r2b5/Arduboy-Version-2/pics/ArduinoISP.jpg

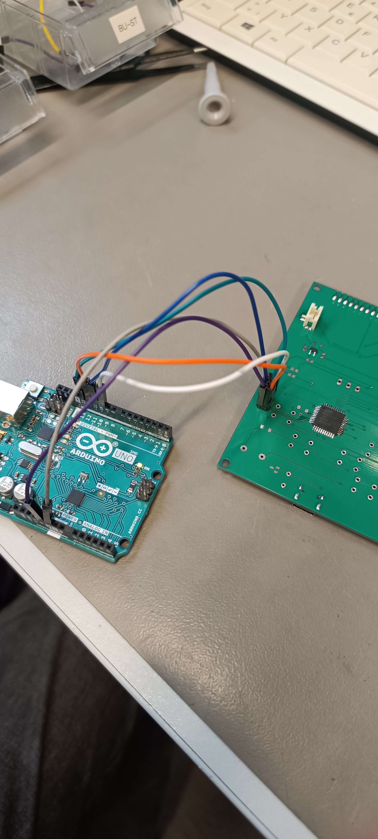
pics/ArduinoISP.jpg
