r2b5/Arduboy-Version-2/src/Tetris/Tetris.ino

#include <Arduboy2.h>

#include "shapes.h"
#include "grid.h"
#include "input_handler.h"

using namespace std;

static Arduboy arduboy;

static shape_actor_t current_actor;

static Grid grid;
static InputHandler input_handler;

static unsigned long time_started;
static unsigned long last_update;

static const unsigned long kDroppingBlockSpeed = 12.0;
static const unsigned long kFallingBlockSpeed = 1.0;

static unsigned long block_speed = kFallingBlockSpeed;

static unsigned int current_score = 0;
bool game_over = false;
uint8_t restartPresses = 0;
bool pause = false;

tetromino_t* random_tetromino()
{
    static const unsigned int num_tetrominos = 8;
    tetromino_t *tetrominos[num_tetrominos] = {
        &SquareBlock,
        &LeftLBlock,
        &RightLBlock,
        &LongBlock,
        &MountainBlock,
        &ZBlock,
        &SBlock,
        &SquareBigBlock,
    };

    long random_idx = random(num_tetrominos);
    return tetrominos[random_idx];
}
void restart_game()
{
    current_score = 0;
    game_over = false;
    restartPresses = 0;
    pause = false;

    block_speed = kFallingBlockSpeed;

    grid.reset();

    current_actor.position = { 5, 0 };
    current_actor.tetromino = random_tetromino();
    current_actor.rotation = 0;
}

void next_block()
{
    grid.commit_actor(current_actor);

    unsigned int lines_cleared = grid.clear_lines();

    switch (lines_cleared)
{
    case 1:
        current_score += 40;
        break;

    case 2:
        current_score += 100;
        break;

    case 3:
        current_score += 300;
        break;

    case 4:
        current_score += 1200;   // TETRIS!
        break;
}

    current_actor.position = { 5, 0 };
    current_actor.tetromino = random_tetromino();
    current_actor.rotation = 0;

    if (grid.actor_collides(current_actor)) {
        game_over = true;
    }
}

void move_current_block_down()
{
    shape_actor_t ghost_actor(current_actor);
    ghost_actor.position.y += 1;

    if (grid.actor_collides(ghost_actor)) {
        next_block();
    } else {
        current_actor.position = ghost_actor.position;
    }
}

void button_handler(uint8_t button, bool down)
{
   if (game_over) {
    if (down && button == A_BUTTON) {
        restartPresses++;

        if (restartPresses >= 2) {
            restart_game();
        }
    }
    return;
}

if (down && button == UP_BUTTON && !game_over)
{
    pause = !pause;
    return;
}

    shape_actor_t ghost_actor(current_actor);

    if (down && button == RIGHT_BUTTON) {
        ghost_actor.position.x += 1;
    }

    if (down && button == LEFT_BUTTON) {
        ghost_actor.position.x -= 1;
    }

    if (down && button == A_BUTTON) {
        ghost_actor.rotation -= 1;
    }

    if (down && button == B_BUTTON) {
        ghost_actor.rotation += 1;
    }

    if (button == DOWN_BUTTON) {
        if (down) {
            block_speed = kDroppingBlockSpeed;
        } else {
            block_speed = kFallingBlockSpeed;
        }
    }

    if (!grid.actor_collides(ghost_actor)) {
        current_actor.position = ghost_actor.position;
        current_actor.rotation = ghost_actor.rotation;
    }
}

void draw_hud(int16_t xpos, int16_t ypos)
{
    const unsigned int kLineHeight = 8;

    arduboy.setTextSize(1);
    arduboy.setCursor(xpos, ypos);

    arduboy.print("Ardutris");

    ypos += kLineHeight + 8;
    arduboy.setCursor(xpos, ypos);

    const char *scoreText = "SCORE";
    arduboy.print(scoreText);

    ypos += kLineHeight;
    arduboy.setCursor(xpos, ypos);

    char scoreString[16];
    sprintf(scoreString, "%u", current_score);
    arduboy.print(scoreString);

    if (game_over) {
        ypos += kLineHeight * 2;
        arduboy.setCursor(xpos, ypos);

        arduboy.print("GAME OVER");
    }

    if (pause)
    {
    ypos += 16;
    arduboy.setCursor(xpos, ypos);
    arduboy.print("PAUSE");
    }
}

void update(unsigned long dt)
{
    input_handler.handle_input(arduboy);

    if (!game_over && !pause)
{
        unsigned long now = millis();
        static unsigned long last_movement = 0;
        if ( (now - last_movement) > (1000 / block_speed) ) {
            // Every second, move interactive actor down by one block
            move_current_block_down();

            last_movement = now;
        }
    }
}

void draw(unsigned long dt)
{
    arduboy.clear();
    arduboy.fillScreen(BLACK);

    Grid display_grid;
    display_grid.copy(grid);

    // Put current actor onto the display grid
    display_grid.commit_actor(current_actor);

    display_grid.draw(arduboy, 20, 2);

    draw_hud(65, 5);

    arduboy.display();
}

void setup()
{
    randomSeed(analogRead(0));

    arduboy.begin();
    arduboy.setFrameRate(60);

    time_started = millis();
    last_update = time_started;

    input_handler.button_handler = button_handler;

    restart_game();
}

void loop()
{
    unsigned long now = millis();
    update(now - last_update);
    draw(now - last_update);
    last_update = now;
}
