r2b5/Arduboy-Version-2/src/arduware-master/arduboy_game/minigame_hurdles.h

#ifndef MINIGAME_HURDLES_H
#define MINIGAME_HURDLES_H

#include "globals.h"
#include <Arduboy2.h>
#include <ArduboyTones.h>

extern Arduboy2 arduboy;
extern ArduboyTones sound;
extern int score;

void doHurdlesGame();

#endif
