r2b5/Arduboy-Version-2/src/Tetris/shapes.h

#ifndef SHAPES_H
#define SHAPES_H

#include "utils.h"

#define SHAPE_BOUNDS_WIDTH  4
#define SHAPE_BOUNDS_HEIGHT 4
#define SHAPE_SIZE (SHAPE_BOUNDS_HEIGHT * SHAPE_BOUNDS_WIDTH)

#define AT(x, y) (SHAPE_BOUNDS_WIDTH * y + x)

struct tetromino_t {
    unsigned int width;
    unsigned int height;

    int shape_data[SHAPE_SIZE];

    int at(unsigned int x, unsigned int y) {
        if (x >= width) return 0;
        if (y >= height) return 0;

        return shape_data[AT(x, y)];
    }

    // returns rotated position offset
    point_t rotated_shape_data(const int rotation, int (*result_shape_data)[16]);
};

static tetromino_t SquareBlock = {
    .width = 2,
    .height = 2,
    .shape_data = {
        1, 1, 0, 0,
        1, 1, 0, 0,
        0, 0, 0, 0,
        0, 0, 0, 0,
    },
};


static tetromino_t SquareBigBlock = {
    .width = 2,
    .height = 3,
    .shape_data = {
        1, 1, 0, 0,
        1, 1, 0, 0,
        1, 1, 0, 0,
        0, 0, 0, 0,
    },
};

static tetromino_t LeftLBlock = {
    .width = 2,
    .height = 3,
    .shape_data = {
        1, 0, 0, 0,
        1, 0, 0, 0,
        1, 1, 0, 0,
        0, 0, 0, 0,
    },
};

static tetromino_t RightLBlock = {
    .width = 2,
    .height = 3,
    .shape_data = {
        0, 1, 0, 0,
        0, 1, 0, 0,
        1, 1, 0, 0,
        0, 0, 0, 0,
    },
};

static tetromino_t LongBlock = {
    .width = 1,
    .height = 4,
    .shape_data = {
        1, 0, 0, 0,
        1, 0, 0, 0,
        1, 0, 0, 0,
        1, 0, 0, 0,
    },
};

static tetromino_t MountainBlock = {
    .width = 3,
    .height = 2,
    .shape_data = {
        0, 1, 0, 0,
        1, 1, 1, 0,
        0, 0, 0, 0,
        0, 0, 0, 0,
    },
};

static tetromino_t ZBlock = {
    .width = 3,
    .height = 2,
    .shape_data = {
        1, 1, 0, 0,
        0, 1, 1, 0,
        0, 0, 0, 0,
        0, 0, 0, 0,
    },
};

static tetromino_t SBlock = {
    .width = 3,
    .height = 2,
    .shape_data = {
        0, 1, 1, 0,
        1, 1, 0, 0,
        0, 0, 0, 0,
        0, 0, 0, 0,
    },
};

struct shape_actor_t
{
public:
    point_t      position;
    tetromino_t *tetromino;
    int          rotation = 0;

    shape_actor_t() {};
    shape_actor_t(const shape_actor_t& a)
        : position(a.position), tetromino(a.tetromino), rotation(a.rotation) {};
};

#endif
