r2b5/Arduboy-Version-2/src/arduware-master/arduboy_game/arduware_title_compressed.h

const uint8_t PROGMEM arduware_title_compressed[] = {
    0x7f, 0x3f, 0x80, 0x65, 0x68, 0xe7, 0xb6, 0xe9, 0x74, 0x76, 0x9d, 0x4e, 
    0x4b, 0x05, 0xbd, 0xa5, 0xe4, 0x36, 0x9d, 0x4e, 0xaa, 0xf0, 0x6c, 0xd3, 
    0xe9, 0x74, 0x9a, 0x7d, 0x3b, 0xb3, 0xdd, 0xa6, 0xd3, 0x5b, 0xe8, 0x39, 
    0xe7, 0xe2, 0xde, 0xb9, 0x6d, 0x1a, 0x41, 0x76, 0x44, 0xe9, 0xf8, 0x97, 
    0x2b, 0xe7, 0x94, 0x53, 0xf2, 0xd3, 0x4b, 0xda, 0x9d, 0x53, 0x32, 0x9d, 
    0x54, 0x4e, 0x2a, 0xc5, 0xfe, 0x5c, 0x2b, 0xb9, 0x4d, 0xa7, 0xb3, 0xbc, 
    0x6d, 0xb7, 0xe9, 0xb4, 0x57, 0x92, 0x9f, 0xcb, 0xcd, 0x9a, 0xd6, 0x29, 
    0x44, 0xb1, 0x2d, 0x95, 0x92, 0xdb, 0xed, 0x7a, 0xc2, 0xf4, 0x96, 0xd9, 
    0x86, 0x26, 0xe7, 0x76, 0x4a, 0x39, 0xa7, 0xe4, 0x4c, 0x69, 0x2e, 0x37, 
    0xe7, 0xce, 0x29, 0x47, 0x94, 0xde, 0xa2, 0x37, 0xe7, 0xc2, 0x95, 0x52, 
    0x52, 0x49, 0x25, 0x95, 0x74, 0x8e, 0x5f, 0x49, 0xba, 0x14, 0xc2, 0x90, 
    0x48, 0x4f, 0x9b, 0x22, 0xe7, 0xc3, 0x93, 0x73, 0x52, 0x29, 0x14, 0x1d, 
    0xad, 0x92, 0x76, 0x5c, 0x39, 0x1d, 0xb6, 0x9e, 0x50, 0xc6, 0xa9, 0x94, 
    0xdc, 0xa2, 0x88, 0x17, 0x53, 0x4a, 0x91, 0xa7, 0x23, 0x46, 0xd1, 0x76, 
    0xbb, 0xdc, 0xb9, 0xed, 0x18, 0xdd, 0x39, 0xe7, 0x9c, 0x73, 0xce, 0x39, 
    0xa7, 0x90, 0xe7, 0x9c, 0x73, 0x4a, 0x2a, 0x39, 0x9b, 0x73, 0xce, 0x29, 
    0xa9, 0xa4, 0x92, 0xdb, 0xd0, 0xb9, 0x55, 0xd2, 0x39, 0xe7, 0x9c, 0x73, 
    0x4e, 0x49, 0x25, 0x9d, 0x73, 0x4e, 0x91, 0x6e, 0x95, 0x74, 0xce, 0x39, 
    0xe7, 0x9c, 0x73, 0x6e, 0xeb, 0x9c, 0x73, 0x0e, 0x67, 0x5b, 0xe7, 0x9c, 
    0x53, 0x48, 0x52, 0xd2, 0x39, 0xe7, 0xa2, 0x57, 0xd2, 0x39, 0x27, 0x95, 
    0x5c, 0x6e, 0x9d, 0x73, 0xce, 0xb9, 0x78, 0x95, 0x73, 0xce, 0x39, 0xe7, 
    0x9c, 0x1b, 0x9b, 0x5b, 0x25, 0x95, 0x74, 0xce, 0x39, 0xe7, 0x9c, 0xdb, 
    0x6e, 0x03, 0xba, 0x20, 
};
